Rota8686/Dynamic-Break-Light-EXPO/Main Project/Expo Photos/Expo Winning Photo.webp

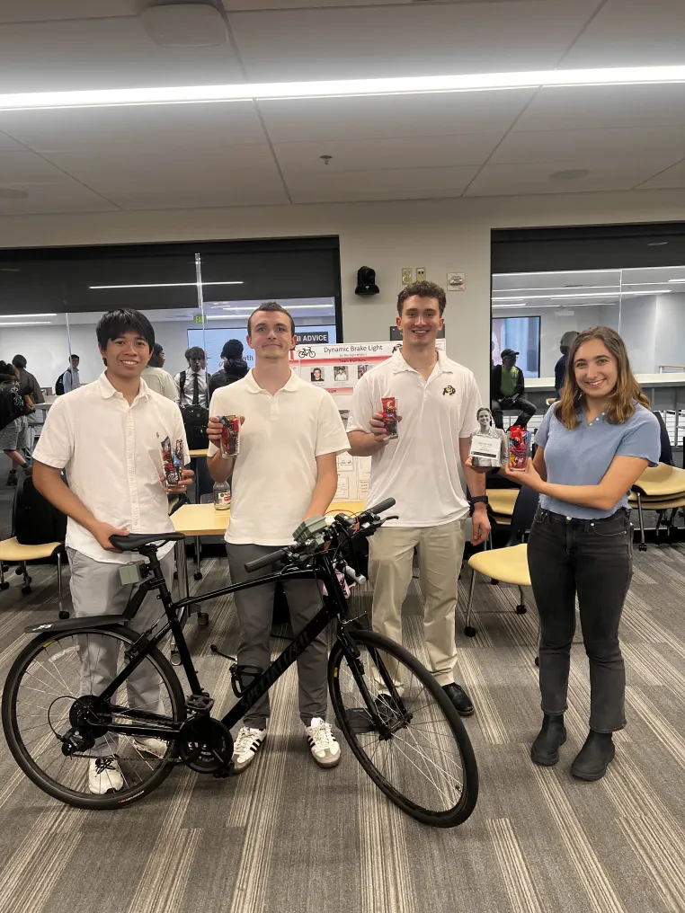
Main Project/Expo Photos/Expo Winning Photo.webp
