Rota8686/Dynamic-Break-Light-EXPO/Main Project/Presentation Materials and Technical Documents/MATLAB Graphs/The Graph for Poster.png

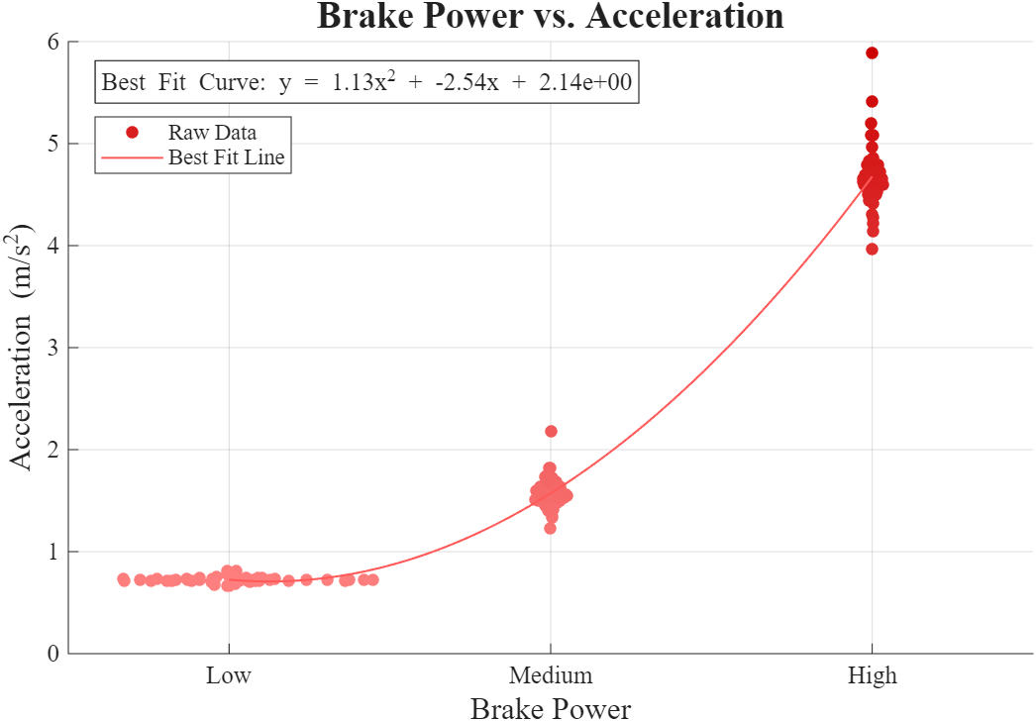
Main Project/Presentation Materials and Technical Documents/MATLAB Graphs/The Graph for Poster.png
