Rota8686/Dynamic-Break-Light-EXPO/Team Members/Expo Photos/Expo Action Shot.webp

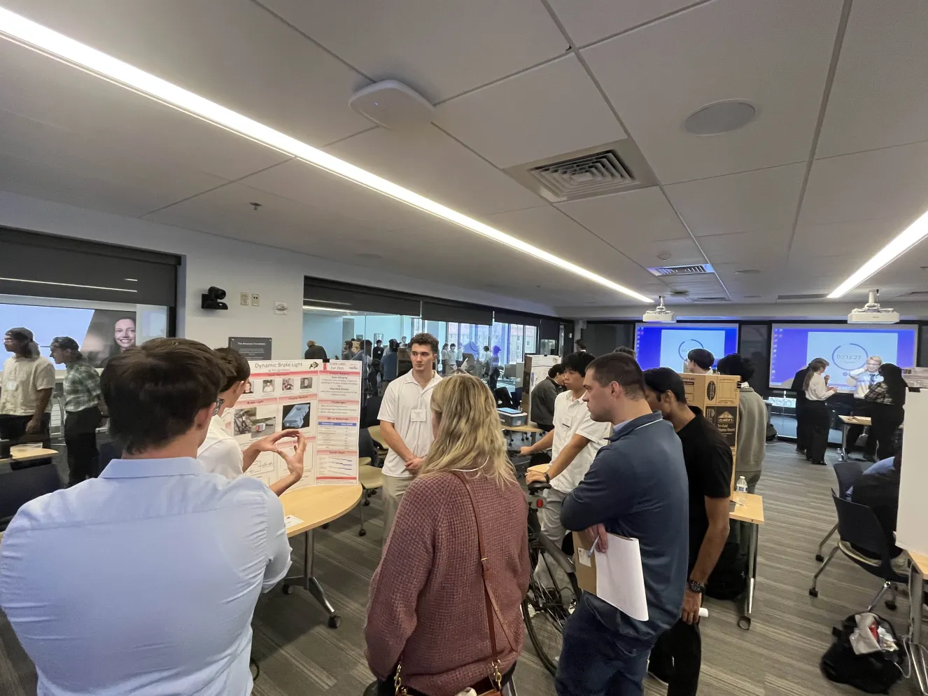
Team Members/Expo Photos/Expo Action Shot.webp
