Rota8686/Dynamic-Break-Light-EXPO/Team Members/Expo Photos/Expo Before Judging.webp

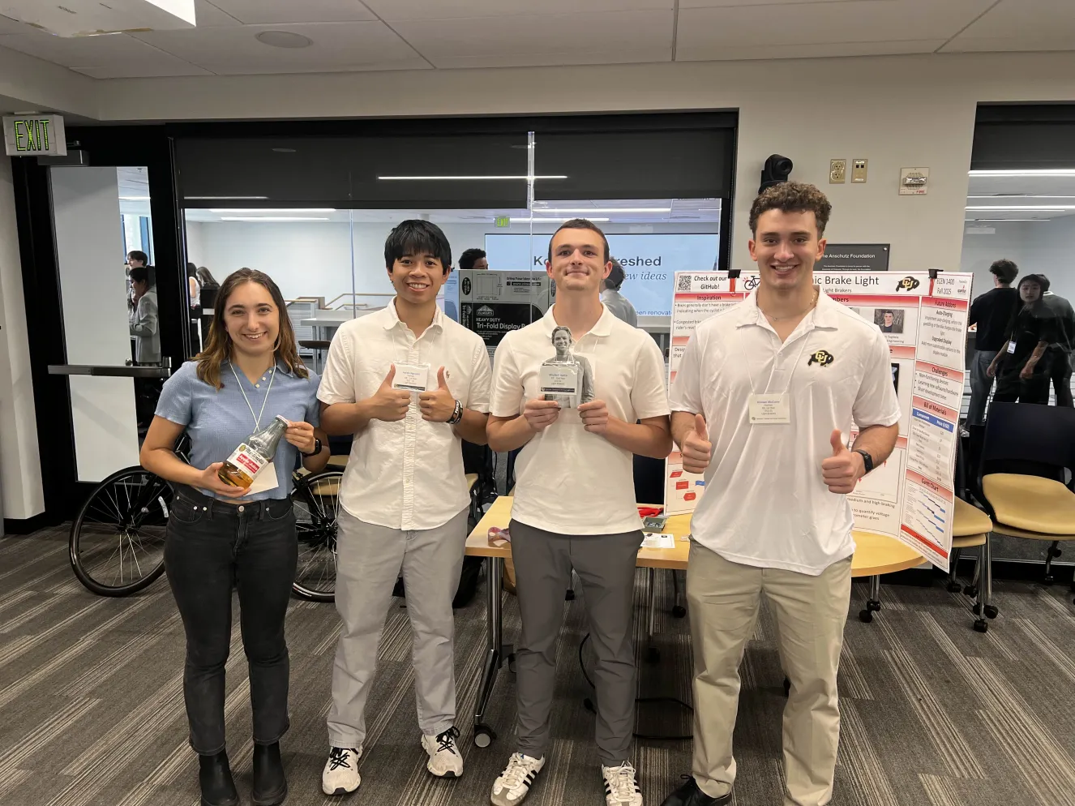
Team Members/Expo Photos/Expo Before Judging.webp
