Rota8686/Dynamic-Break-Light-EXPO/Team Members/Mitchell Vallis/Mitchell Vallis With His Loot.webp

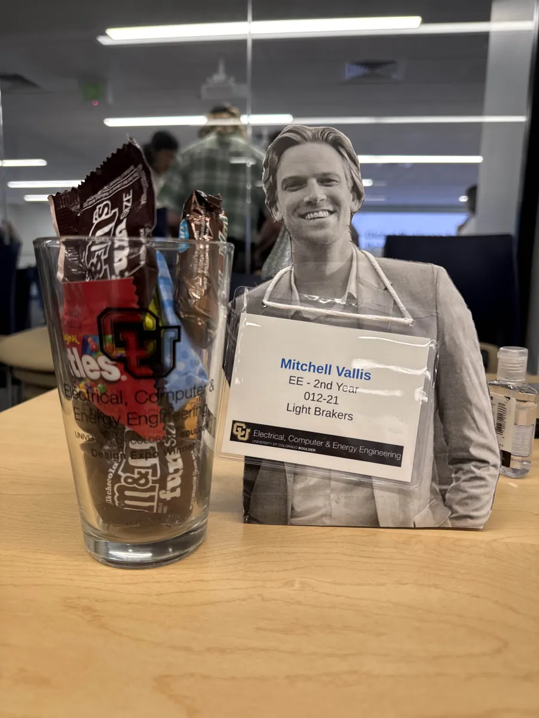
Team Members/Mitchell Vallis/Mitchell Vallis With His Loot.webp
