Rota8686/Dynamic-Break-Light-EXPO/Main Project/Presentation Materials and Technical Documents/Gantt Chart.png

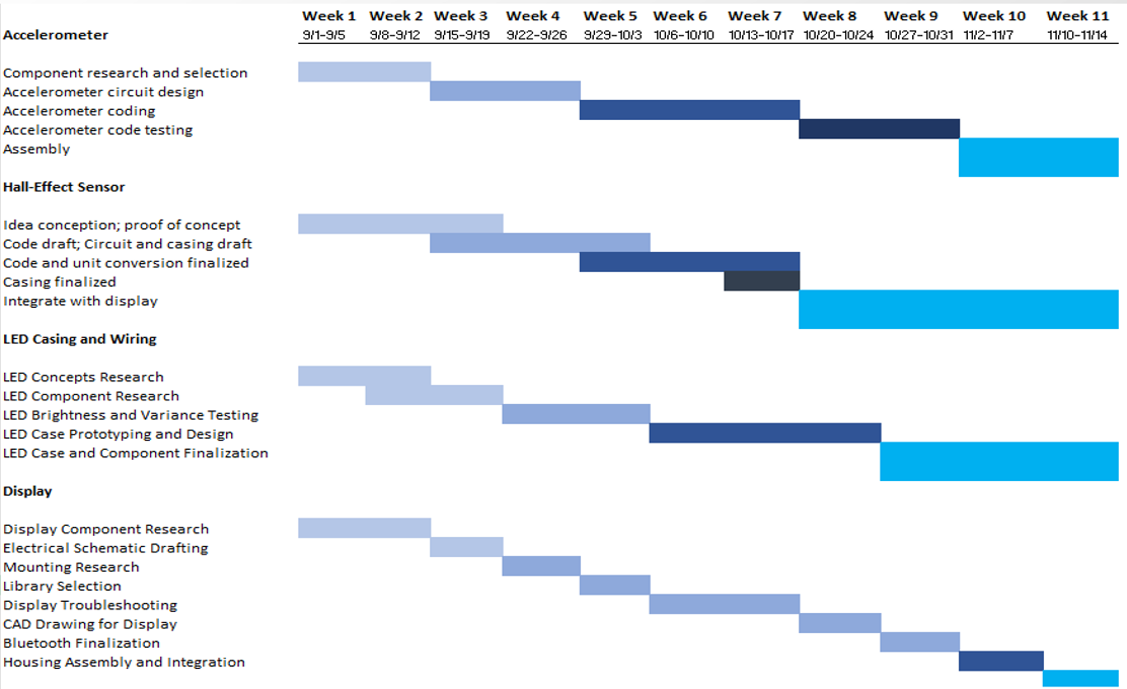
Main Project/Presentation Materials and Technical Documents/Gantt Chart.png
