Rota8686/Dynamic-Break-Light-EXPO/Main Project/Presentation Materials and Technical Documents/LED Module Block Diagram.png

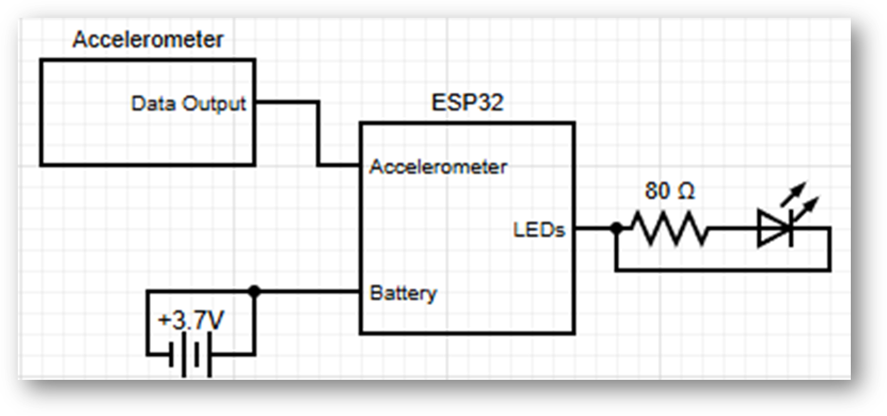
Main Project/Presentation Materials and Technical Documents/LED Module Block Diagram.png
