Rota8686/Dynamic-Break-Light-EXPO/Main Project/Presentation Materials and Technical Documents/MATLAB Graphs/bp_vs_a.png

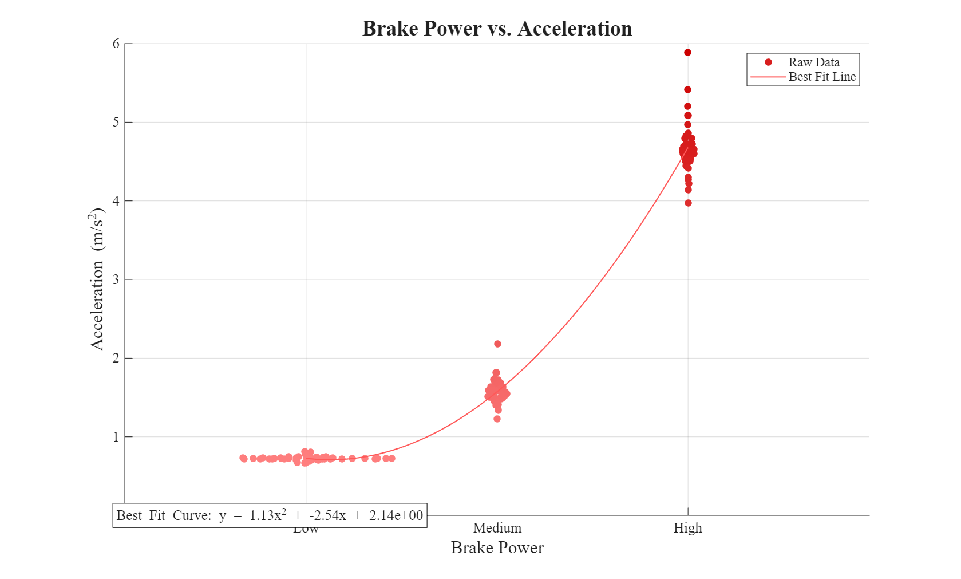
Main Project/Presentation Materials and Technical Documents/MATLAB Graphs/bp_vs_a.png
