Rota8686/Dynamic-Break-Light-EXPO/Main Project/Presentation Materials and Technical Documents/MATLAB Graphs/d_vs_tts.png

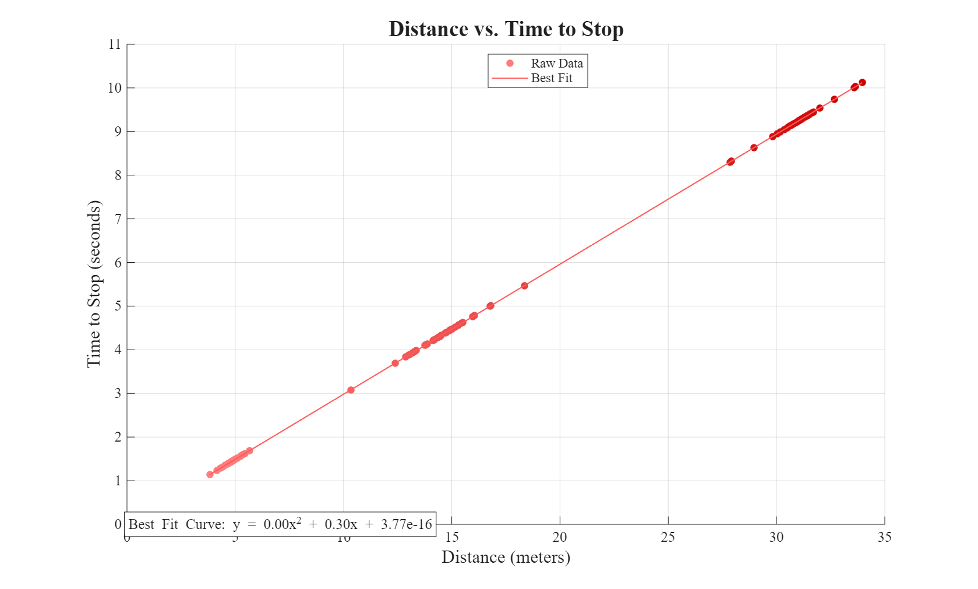
Main Project/Presentation Materials and Technical Documents/MATLAB Graphs/d_vs_tts.png
