Rota8686/Dynamic-Break-Light-EXPO/Main Project/Presentation Materials and Technical Documents/Software Flow Chart.png

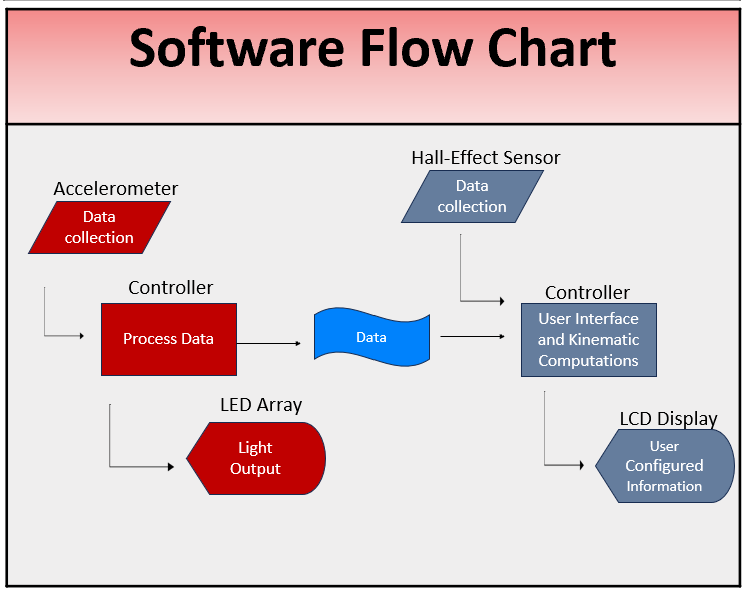
Main Project/Presentation Materials and Technical Documents/Software Flow Chart.png
