Rota8686/Dynamic-Break-Light-EXPO/Main Project/Soldering and Assembly/Demo Soldering.webp

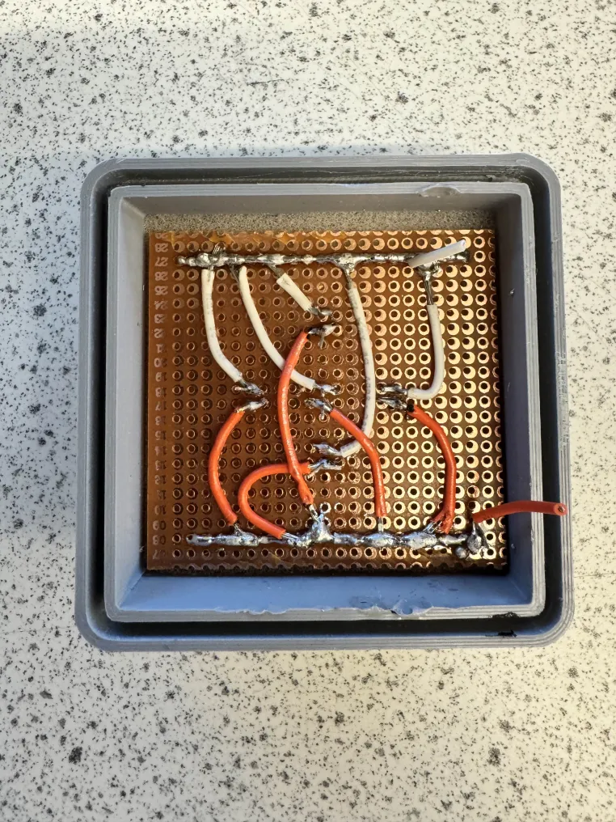
Main Project/Soldering and Assembly/Demo Soldering.webp
