Rota8686/Dynamic-Break-Light-EXPO/Main Project/Soldering and Assembly/Display Soldering Top.webp

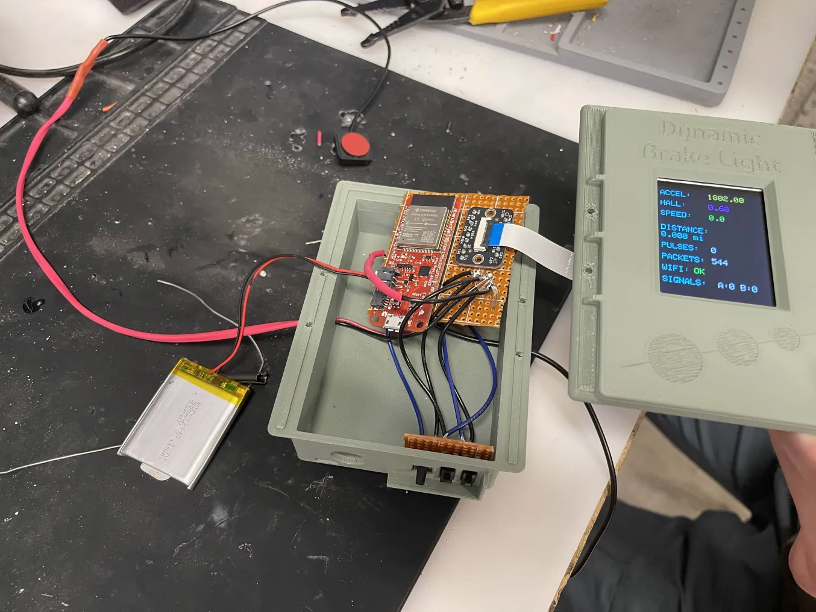
Main Project/Soldering and Assembly/Display Soldering Top.webp
