Rota8686/Dynamic-Break-Light-EXPO/Main Project/Soldering and Assembly/LED Module Interal Lay Out.webp

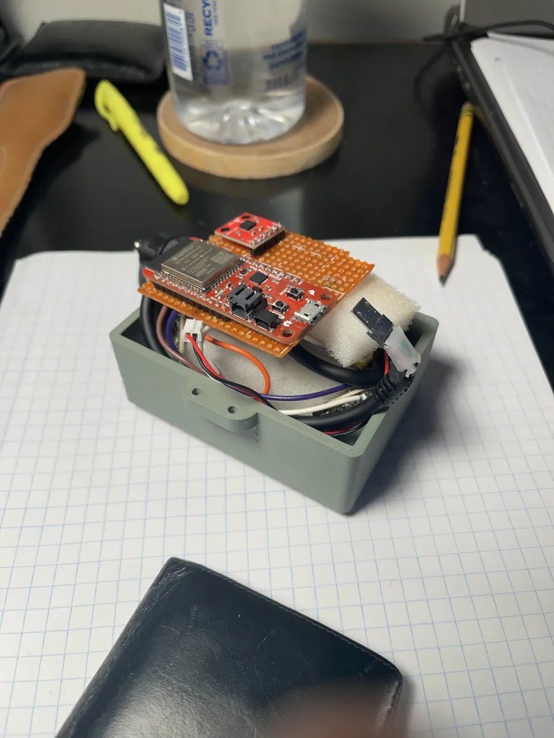
Main Project/Soldering and Assembly/LED Module Interal Lay Out.webp
