Rota8686/Dynamic-Break-Light-EXPO/Main Project/Soldering and Assembly/LED Module Picture.webp

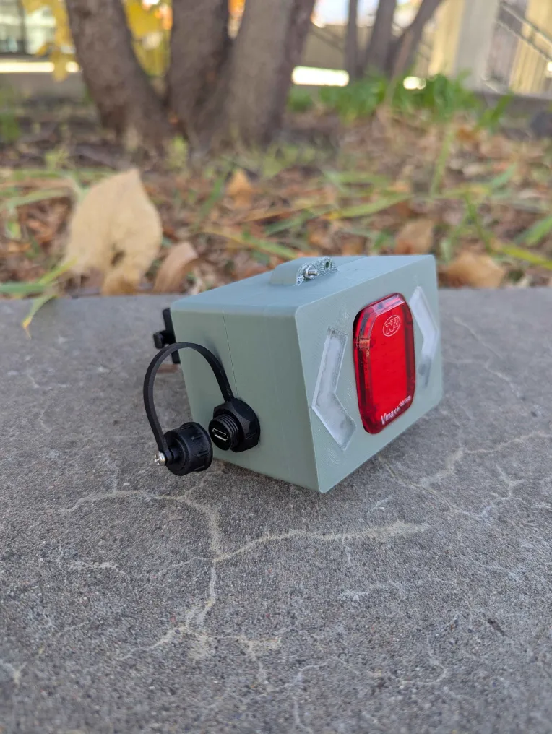
Main Project/Soldering and Assembly/LED Module Picture.webp
