Rota8686/Dynamic-Break-Light-EXPO/Main Project/Soldering and Assembly/Mounted Display Module.webp

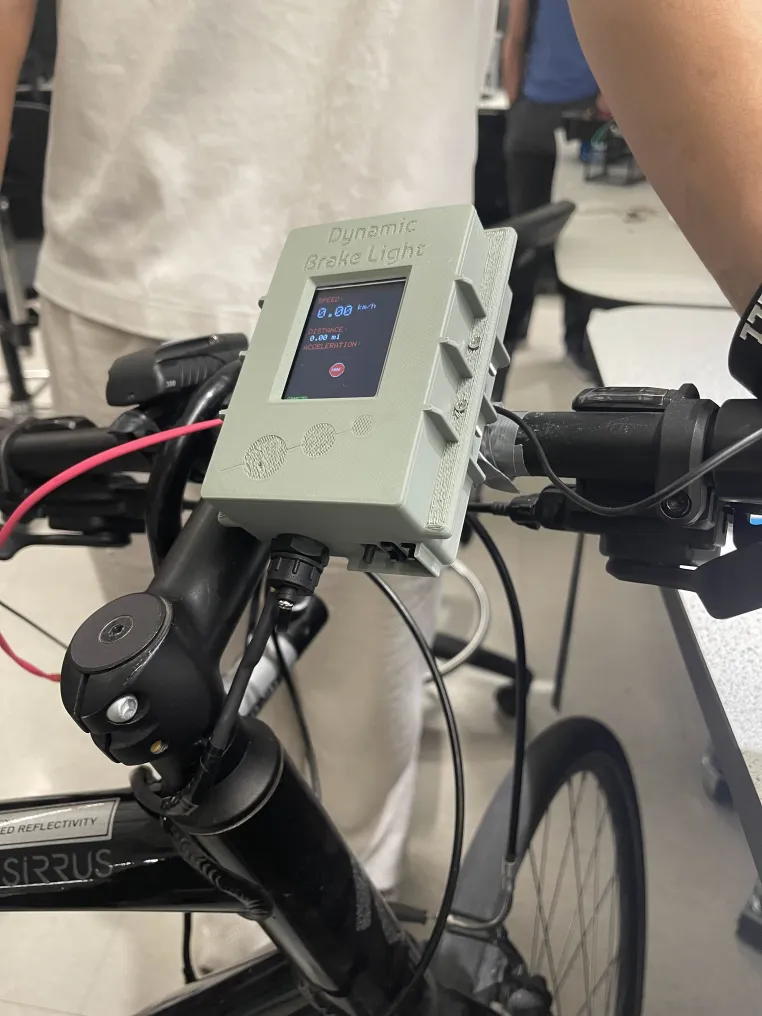
Main Project/Soldering and Assembly/Mounted Display Module.webp
