Rota8686/Dynamic-Break-Light-EXPO/Main Project/Soldering and Assembly/Turn Signal Soldering.webp

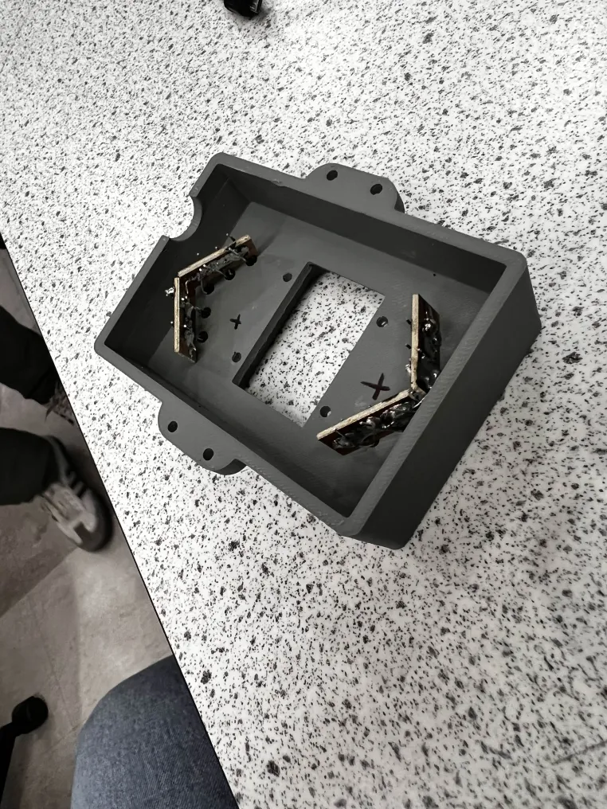
Main Project/Soldering and Assembly/Turn Signal Soldering.webp
