Rota8686/Dynamic-Break-Light-EXPO/Main Project/Presentation Materials and Technical Documents/Display Module Soldering Schematic.kicad_sch

## KiCad design Main Project/Presentation Materials and Technical Documents/Display Module Soldering Schematic.kicad_sch (2025-11-15)

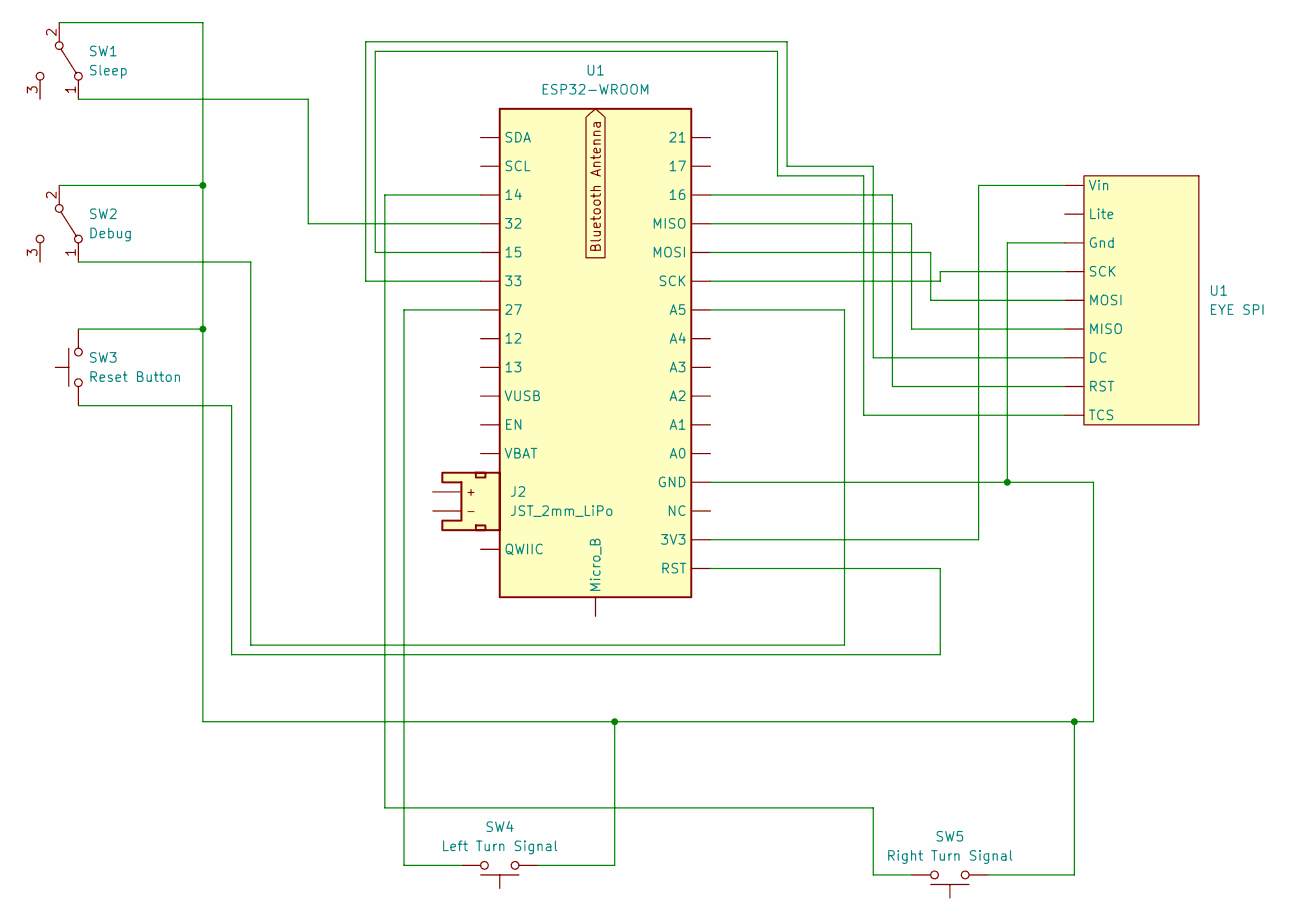
[picture p44: schematic Display Module Soldering Schematic.kicad_sch]

Parts:
J2: JST_2mm_LiPo; JST_1x02_P2.0mm_Horizontal_SMD
SW1: Sleep; Slide_DPDT_SMD_7.2x3.5mm; Mrg Part# AYZ0202
SW2: Debug; Slide_DPDT_SMD_7.2x3.5mm; Mrg Part# AYZ0202
SW3: Reset Button; Push_SMD_6x3.5mm; Mfg Part# 8-004 SMD Button 8x3.6mm Height=2.5mm
SW4: Left Turn Signal; Push_SMD_6x3.5mm; Mfg Part# 8-004 SMD Button 8x3.6mm Height=2.5mm
SW5: Right Turn Signal; Push_SMD_6x3.5mm; Mfg Part# 8-004 SMD Button 8x3.6mm Height=2.5mm
U1: EYE SPI

Connections:
unnamed: SW1.1 (A), U1. (SDA)
unnamed: SW1.2 (B), SW2.2 (B), SW3.2, SW4.1, SW5.1, U1. (SDA)
unnamed: SW2.1 (A), U1. (SDA)
unnamed: SW3.1, U1. (SDA)
unnamed: SW4.2, U1. (SDA)
unnamed: SW5.2, U1. (SDA)
unnamed: U1. (SDA), U1.15 (GND), U1.38 (GND), U1.49.1 (GND), U1.49.2 (GND), U1.49.3 (GND), U1.49.4 (GND), U1.49.5 (GND), U1.49.6 (GND), U1.49.7 (GND), U1.49.8 (GND), U1.49.9 (GND)
