Rota8686/Dynamic-Break-Light-EXPO/Main Project/Presentation Materials and Technical Documents/Reactive_Break_Light_Schematic.kicad_sch

## KiCad design Main Project/Presentation Materials and Technical Documents/Reactive_Break_Light_Schematic.kicad_sch (2025-11-15)

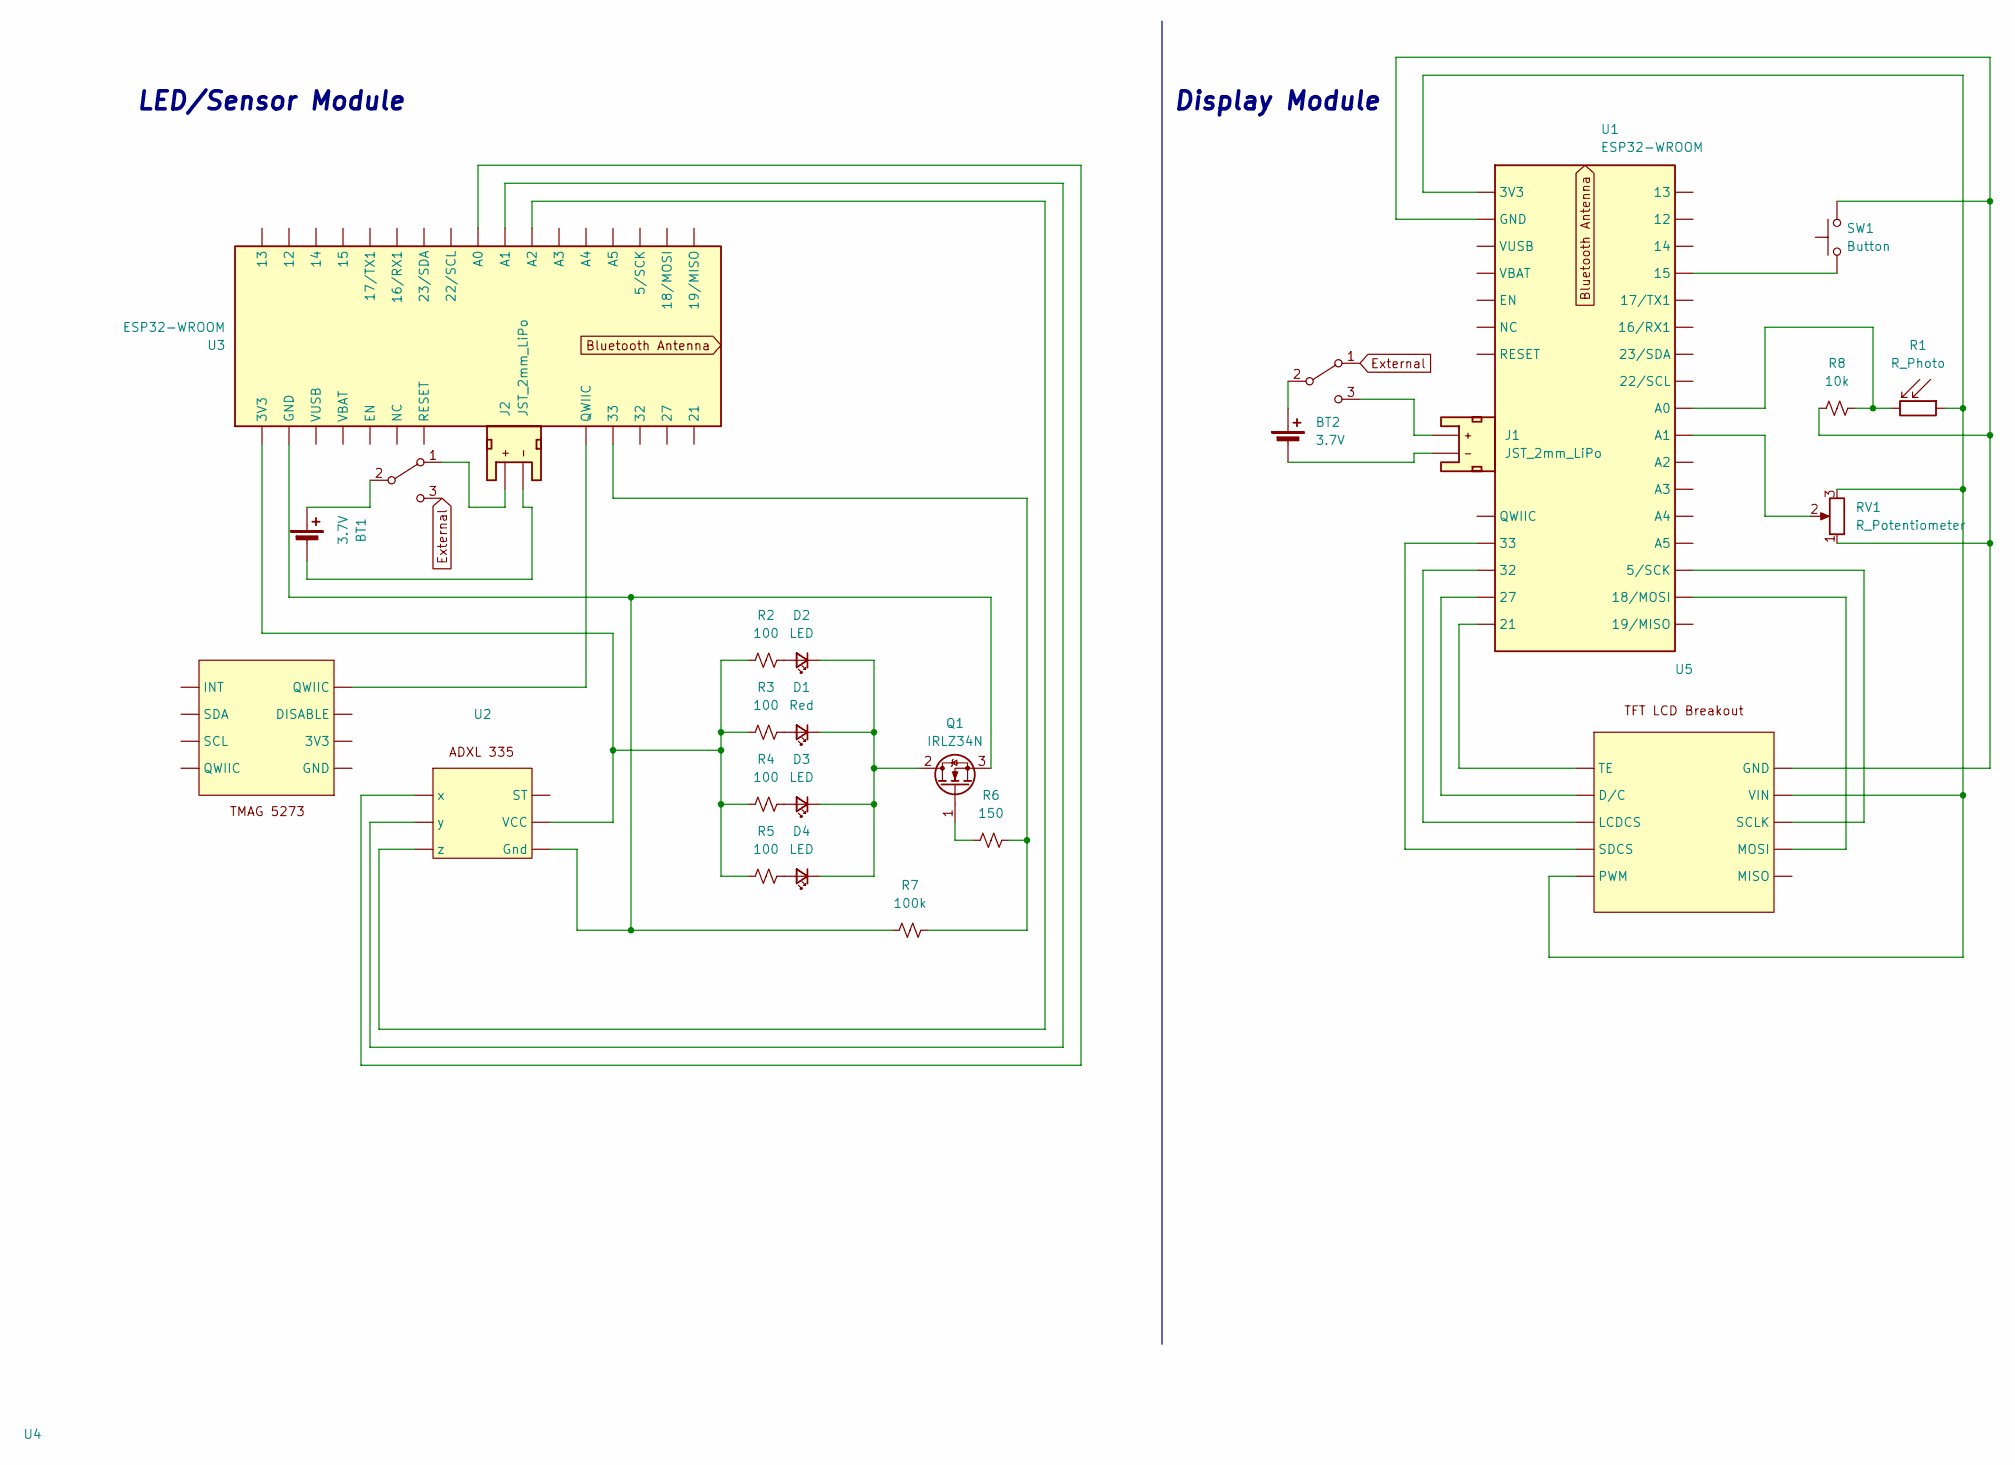
[picture p45: schematic Reactive_Break_Light_Schematic.kicad_sch]

Parts:
BT1, BT2: 3.7V
D1: Red; LED_5mm_PTH_Red_NoSilk
D2, D3, D4: LED; LED_0603_1608Metric
J1, J2: JST_2mm_LiPo; JST_1x02_P2.0mm_Horizontal_SMD
Q1: IRLZ34N; TO-220-3_Vertical
R1: R_Photo
R2, R3, R4, R5: 100; R_0402_1005Metric
R6: 150; R_0402_1005Metric
R7: 100k; R_0402_1005Metric
R8: 10k; R_0402_1005Metric
RV1: R_Potentiometer
SW1: Button; Push_SMD_6x3.5mm; Mfg Part# 8-004 SMD Button 8x3.6mm Height=2.5mm
SW2: SPDT_Slide_SMD_9.0x3.6mm; Slide_DPDT_SMD_9.0x3.6mm
SW3: Flip Switch; Slide_DPDT_SMD_9.0x3.6mm
U1, U3: ESP32-WROOM; ESP32-WROOM-32D-DFM_Paste
U2, U4, U5: (no value)

Connections:
External: SW2.1 (A), SW3.3 (C)
unnamed: BT1.1 (+), SW3.2 (B)
unnamed: BT1.2 (-), J2.1 (-)
unnamed: BT2.1 (+), SW2.2 (B)
unnamed: BT2.2 (-), J1.1 (-)
unnamed: D1.1 (K), D2.1 (K), D3.1 (K), D4.1 (K), Q1.2 (D)
unnamed: D1.2 (A), R3.2
unnamed: D2.2 (A), R2.2
unnamed: D3.2 (A), R4.2
unnamed: D4.2 (A), R5.2
unnamed: J1.2 (+), SW2.3 (C)
unnamed: J2.2 (+), SW3.1 (A)
unnamed: Q1.1 (G), R6.1
unnamed: Q1.3 (S), R7.1, U2., U3. (3V3)
unnamed: R1.1, RV1.3, U1. (3V3), U5.
unnamed: R1.2, R8.2, U1. (3V3)
unnamed: R2.1, R3.1, R4.1, R5.1, U2., U3. (3V3)
unnamed: R6.2, R7.2, U3. (3V3)
unnamed: R8.1, RV1.1, SW1.2, U1. (3V3), U5.
unnamed: RV1.2, U1. (3V3)
unnamed: SW1.1, U1. (3V3)
unnamed: SW3.5, U3. (3V3)
unnamed: U1.15 (GND), U1.38 (GND), U1.49.1 (GND), U1.49.2 (GND), U1.49.3 (GND), U1.49.4 (GND), U1.49.5 (GND), U1.49.6 (GND), U1.49.7 (GND), U1.49.8 (GND), U1.49.9 (GND)
unnamed: U1. (3V3), U5.
unnamed: U2., U3. (3V3)
unnamed: U3.15 (GND), U3.38 (GND), U3.49.1 (GND), U3.49.2 (GND), U3.49.3 (GND), U3.49.4 (GND), U3.49.5 (GND), U3.49.6 (GND), U3.49.7 (GND), U3.49.8 (GND), U3.49.9 (GND)
unnamed: U3. (3V3), U4.

Notes on the sheet:
Display Module
LED/Sensor Module
